MRU-Earth-and-Enviromental-Science/Low-Cost-Sensors/drone_esp32/src/macAddress.cpp

// uncomment the code and comment out main.cpp code to use this file for MAC address reading
// #include <WiFi.h>
// #include <esp_wifi.h>

// void readMacAddress()
// {
//     uint8_t baseMac[6];
//     esp_err_t ret = esp_wifi_get_mac(WIFI_IF_STA, baseMac);
//     if (ret == ESP_OK)
//     {
//         Serial.printf("%02x:%02x:%02x:%02x:%02x:%02x\n",
//                       baseMac[0], baseMac[1], baseMac[2],
//                       baseMac[3], baseMac[4], baseMac[5]);
//     }
//     else
//     {
//         Serial.println("Failed to read MAC address");
//     }
// }

// void setup()
// {
//     Serial.begin(115200);

//     WiFi.mode(WIFI_STA);
//     WiFi.begin();

//     Serial.print("[DEFAULT] ESP32 Board MAC Address: ");
//     readMacAddress();
// }

// void loop()
// {
// }
