MRU-Earth-and-Enviromental-Science/Low-Cost-Sensors/drone_esp32/include/Temp.h

// Temp.h
#ifndef TEMP_H
#define TEMP_H

#include <Arduino.h>
#include <DHT.h>

#define DHTPIN 13
#define DHTTYPE DHT11

extern DHT dht;

void readTemperatureHumidity(float &temperature, float &humidity);

#endif // TEMP_H
